gx1400/kicad_foxhunt_batterytest/_docs/firmware/README.md

# Firmware docs (reserved)

Placeholder — no firmware exists yet. Once the PlatformIO project (`src/`) is started, its
design docs (architecture, module layout, protocol notes, etc.) go here.
