gx1400/kicad_foxhunt_batterytest/_docs/sourcing/task1_lcsc_crossreference.md

# BOM / LCSC Cross-Reference — Results

Verification method: see [`_agent_tasks/bom_property_audit.md`](../../_agent_tasks/bom_property_audit.md).
Re-run after any significant schematic change — reference designators on this project have
already churned across three renumbering passes, so treat every designator below as a snapshot
of this date, not a durable identifier.

**Result: 93 of 126 real components have complete `Manf`/`MPN`/`LCSC Part #` data. Zero
Value/MPN/Manufacturer mismatches found against real LCSC data** across every part checked.

## Fixed since the prior pass

- **U13 (CH340C)**: now has Manf=WCH, MPN=CH340C, LCSC=`C84681` — verified correct.
- **R7 (80.6k)**: Manf typo ("YAGE") corrected to YAGEO; MPN=`RT0603BRE0780K6L`, LCSC=`C862291` —
  verified correct.
- **R5, R8 (30.1k)**: both now complete, LCSC=`C137745` — verified correct.
- **R14 (1k)**: LCSC=`C95781` now present.
- **BT2**: now carries the same LCSC ID as BT1 (`C5339083`) instead of being blank — the "copy
  over" is done, though see the standing exception below (that ID is still delisted).

## Open items

- [ ] **Re-run the full audit** (`_agent_tasks/bom_property_audit.md`) against the current
  component set — two more waves of new real parts have landed since the last formal pass:
  - VRAW soft-latch and PCF8563 RTC circuits (~15 parts): Q5/Q8 AO3407A, Q6/Q7 BSS138,
    D2/D3 Nexperia BAS116LT1G, BT3 CR2032, U14 PCF8563T/5 `C7440`, Y2 NDK
    NX3215SA-32.768K-STD-MUA-9 `C519280`, R29–R33, C43, JP24, SW3.
  - Expansion-IO section (~20 parts): U15 PCA9555PWR `C2864778`, U16 CAT24C32YI-GT3
    `C94264`, D7–D10 Kingbright LEDs (`C5569446`/`C5366382`/`C5879058`/`C5588998`),
    R34–R42, SW4/SW7–SW10, J4–J7, JP27, C46–C49, C51.
  - Also re-verify U9/U12 now carry TI `LM1117IMPX-3.3/NOPB` (`C23984`) — swapped from
    AMS1117-3.3 since the last audit pass.
  - D4 (WS2812B-B/W, Worldsemi, `C114586`) and its local bypass cap C52, on
    `mcu-esp32.kicad_sch`.

  Each was individually checked against its real datasheet/LCSC listing during design (not
  fabricated placeholders), but none have been through this doc's formal tool-assisted
  audit workflow yet — worth confirming footprint/manufacturer consistency the same way as
  everything below, rather than trusting ad hoc verification.

## Resolved since last pass (2026-09-19)

- **The shunt resistor's footprint/manufacturer mismatch (R13, the 0.0025Ω current-sense shunt —
  was R11, then R4, then R13 across three renumbering passes; identify by function, not
  designator).** No longer borrowing the generic `R_Shunt_Vishay_WSK2512_6332Metric_T2.21mm`
  library footprint. Replaced with a purpose-built footprint
  (`kicad_gx_library:RES-SMD_L6.4-W3.2-R2512_Sense4Pin`) matching the actual sourced part
  (Milliohm `HoJLR2512-3W-2.5mR-1%`, LCSC `C2904234`, 2512 case). Verified the raw `.kicad_mod`
  directly: correct 4-pad Kelvin-sense layout (force pads 1/4 at 2×3.3mm, sense pads 2/3 at
  0.5×0.5mm sitting at the edge of their respective force pad) with
  `(net_tie_pad_groups "1,2" "3,4")` so DRC doesn't flag the intentional pad-group ties as shorts.
  Worth a final sanity check that the 2×3.3mm force-pad dimensions match Milliohm's own datasheet,
  but the manufacturer-mismatch risk itself is gone now that this isn't a generic Vishay-library
  footprint.

- **U1, U2, U3 field naming**: normalized from `easyeda2kicad`'s defaults (`Manufacturer`,
  `LCSC Part`) to this project's convention (`Manf`, `LCSC Part #`) — verified via fresh netlist,
  all three consistent (Manf=TI, LCSC Part #=C485916), `Source`/`Imported` traceability fields
  preserved.
- **Stage 1 ILM (R8, 30.1kΩ)**: confirmed intentional — was undersized at the prior 51.1kΩ for
  the combined battery-side current across both downstream rails, per the same reasoning noted
  in the last pass.

## Standing exceptions (see the playbook for the full list/reasoning)

- BT1/BT2: LCSC `C5339083` delisted, known and accepted.
- The two 2W THT bleed resistors (currently R22/R23): intentionally SparkFun-sourced, not
  JLCPCB-verifiable by design.
- Capacitor voltage in `Value` is a minimum, not exact.
- Standard company-name abbreviations (TI/Texas Instruments, etc.) are not mismatches.
- Non-LCSC-sourced parts (F2, J1, J2, etc.) are fine as-is if self-consistent.

## Informational — no action needed

- **F2, J1, J2**: Manf+MPN present and self-consistent (MULTICOMP PRO, Anderson Power Products,
  PHOENIX CONTACT respectively), no LCSC Part# — legitimately non-LCSC-sourced.
- **22 jumpers + 3 test points**: no sourcing fields, expected for generic mechanical parts.
